peng-zhihui/PocketLCD/5.Images/img2.jpg

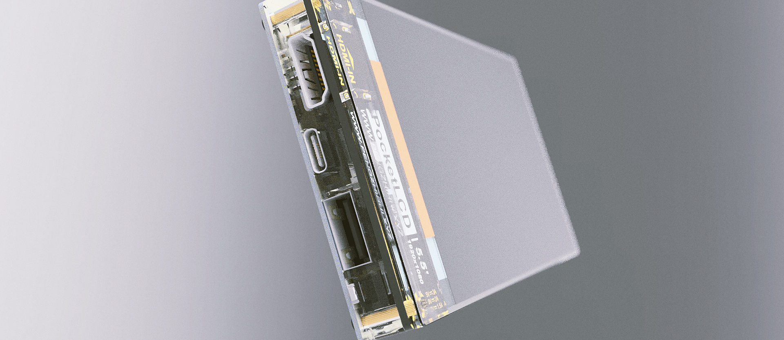
5.Images/img2.jpg
