peng-zhihui/PocketLCD/5.Images/img3.jpg

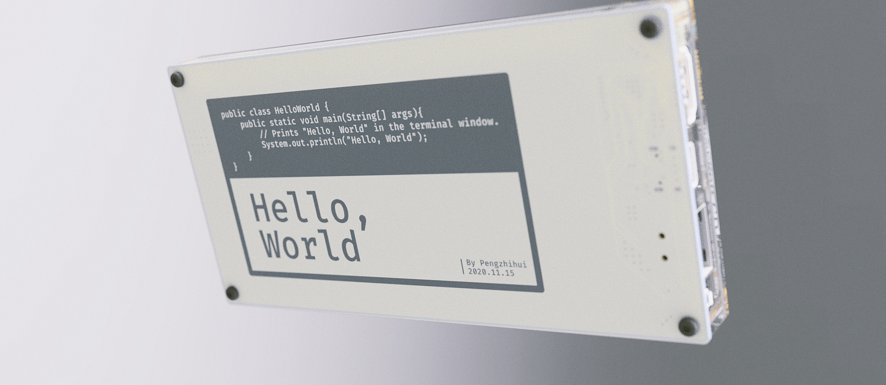
5.Images/img3.jpg
