peng-zhihui/PocketLCD/5.Images/img4.jpg

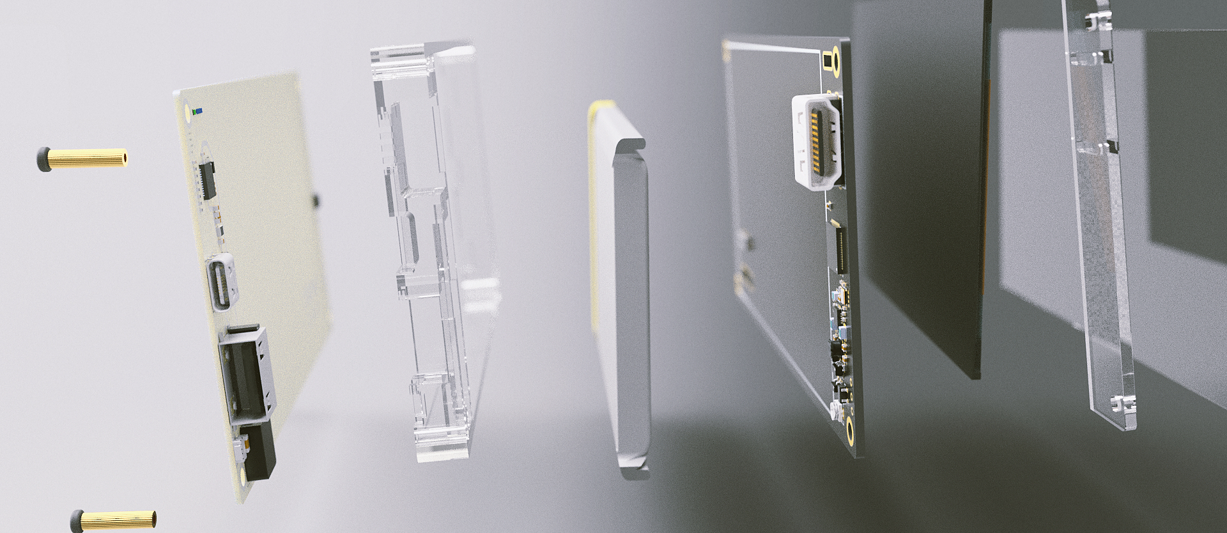
5.Images/img4.jpg
